SHARPENTIERS/MZ-SD2CMT/src/drivers/sdcard.h

#ifndef SD2CMT2_SDCARD_H
#define SD2CMT2_SDCARD_H

#include <stdbool.h>
#include <stdint.h>

#define SDCARD_ENTRY_NAME_MAX 64U

typedef struct
{
    char name[SDCARD_ENTRY_NAME_MAX];
    bool is_dir;
    /* SdFat returns an empty string when the complete LFN does not fit. */
    bool name_too_long;
    uint32_t size;

    /* Physical order in the directory scan. It is only a stable tie-breaker
       when two entries compare equal by name and type. */
    uint16_t source_index;

} sdcard_entry_t;

void sdcard_early_prepare_pins(void);

bool sdcard_init(void);
bool sdcard_is_inserted(void);
bool sdcard_detect_poll(void);
bool sdcard_detect_consume_inserted_edge(void);
bool sdcard_detect_removed_edge(void);

/* Force a full SdFat/SPI initialization even if the card was mounted before.
   Used after card insertion/retry before the browser reopens root. */
bool sdcard_reinitialize(void);

bool sdcard_is_mounted(void);

uint16_t sdcard_count_entries(const char *path, uint16_t max_entries);

bool sdcard_read_entry_by_index(const char *path, uint16_t index, sdcard_entry_t *entry);

/*
    Single-pass browser bootstrap: opens path once, counts up to max_entries and
    returns the first alphabetical item from that same directory scan.  An empty
    directory is successful with *entry_count == 0 and an empty *first_entry.
    This avoids opening root once for counting and again for selection directly
    after SD-card initialization.
*/
bool sdcard_scan_directory_first_sorted(const char *path,
                                        uint16_t max_entries,
                                        uint16_t *entry_count,
                                        sdcard_entry_t *first_entry);
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
